ldijkman/ART-ESP32-Touch-TFT-Thermostat/images/Art_ESP32_Smart_Thermostat_webserver.jpg

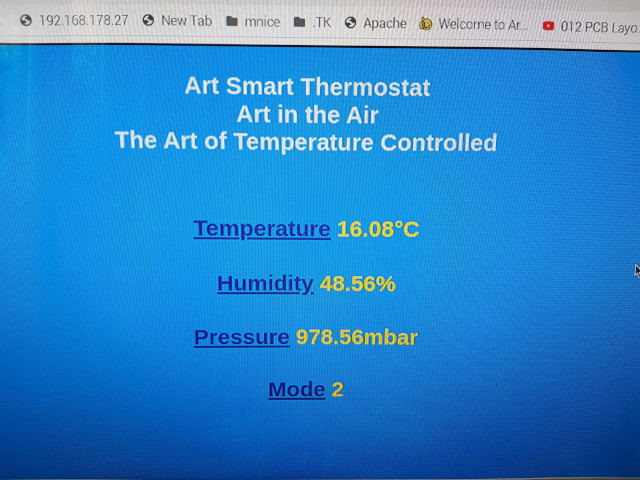
images/Art_ESP32_Smart_Thermostat_webserver.jpg
