ldijkman/ART-ESP32-Touch-TFT-Thermostat/images/art_in_the_air.jpg

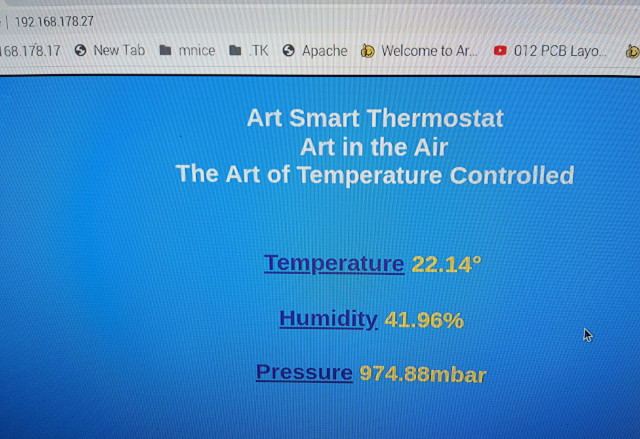
images/art_in_the_air.jpg
