ldijkman/ART-ESP32-Touch-TFT-Thermostat/images/art_ip_adres.jpg

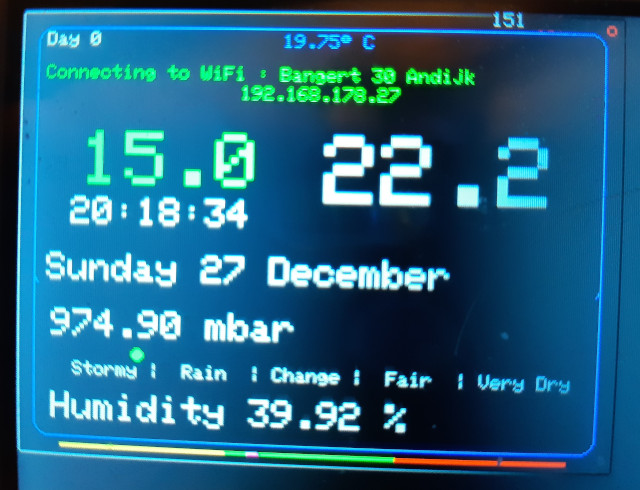
images/art_ip_adres.jpg
