ldijkman/ART-ESP32-Touch-TFT-Thermostat/images/Art_remote_mode_control.jpg

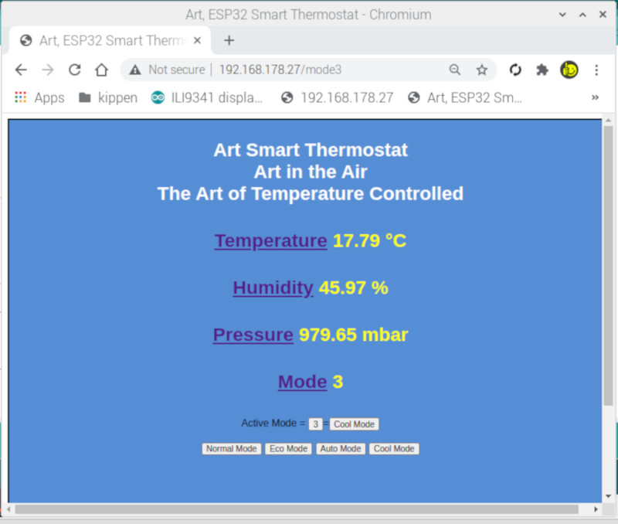
images/Art_remote_mode_control.jpg
