ldijkman/ART-ESP32-Touch-TFT-Thermostat/images/arts_memory_directory_listing.jpg

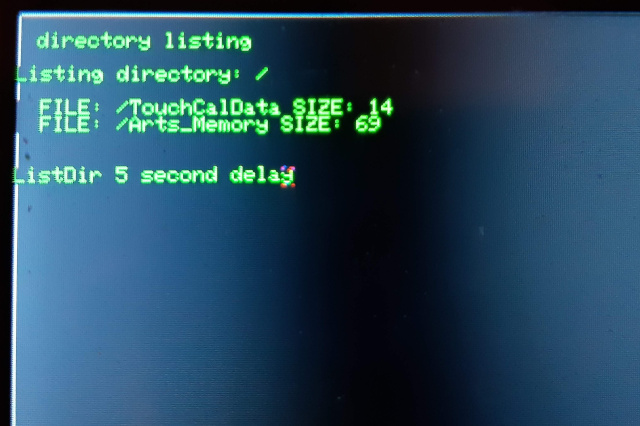
images/arts_memory_directory_listing.jpg
