ldijkman/ART-ESP32-Touch-TFT-Thermostat/images/arts_memory_save_read_write_variables_spiffs_file.jpg

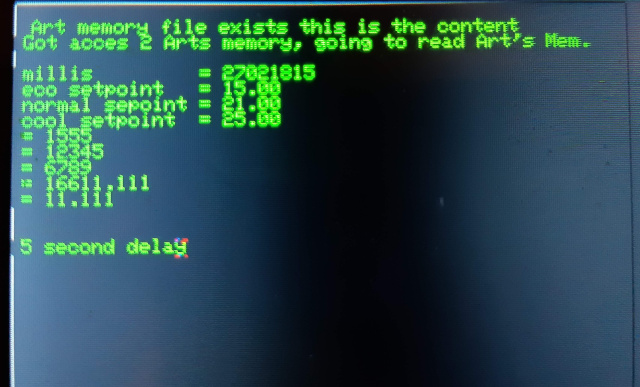
images/arts_memory_save_read_write_variables_spiffs_file.jpg
