ldijkman/ART-ESP32-Touch-TFT-Thermostat/images/ESP32-38PIN_Arduino_settings.jpg

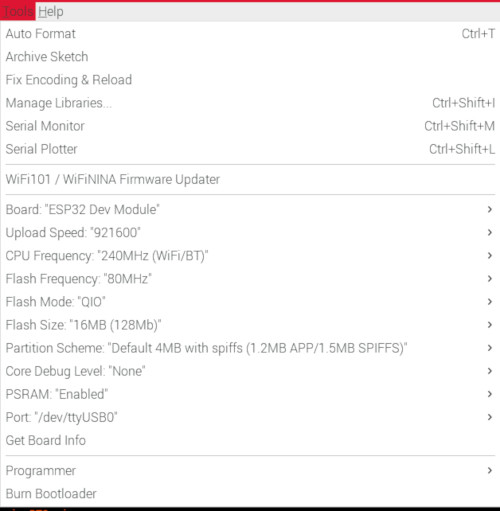
images/ESP32-38PIN_Arduino_settings.jpg
