ldijkman/ART-ESP32-Touch-TFT-Thermostat/images/screenshot-arduino-tk-alarm-DailyAlarms-com-php-1609703187235.png

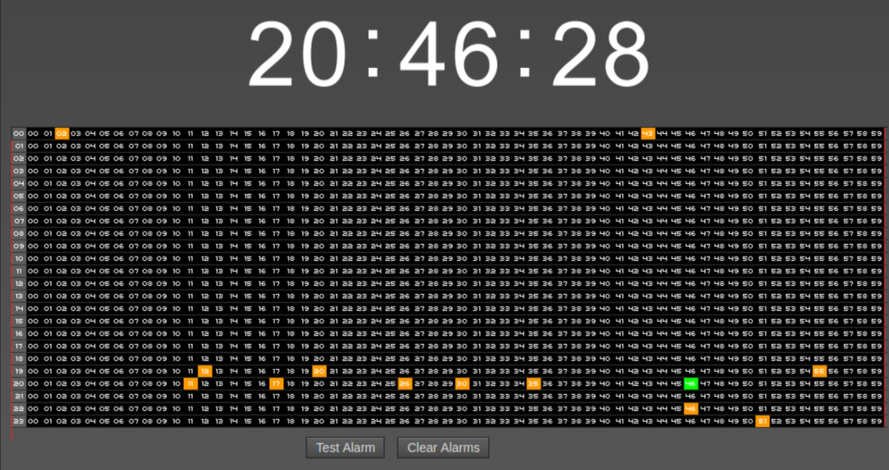
images/screenshot-arduino-tk-alarm-DailyAlarms-com-php-1609703187235.png
