ldijkman/ART-ESP32-Touch-TFT-Thermostat/test/art_test_1/Remote_WiFi_Sense_Switch/20210912_184351.jpg

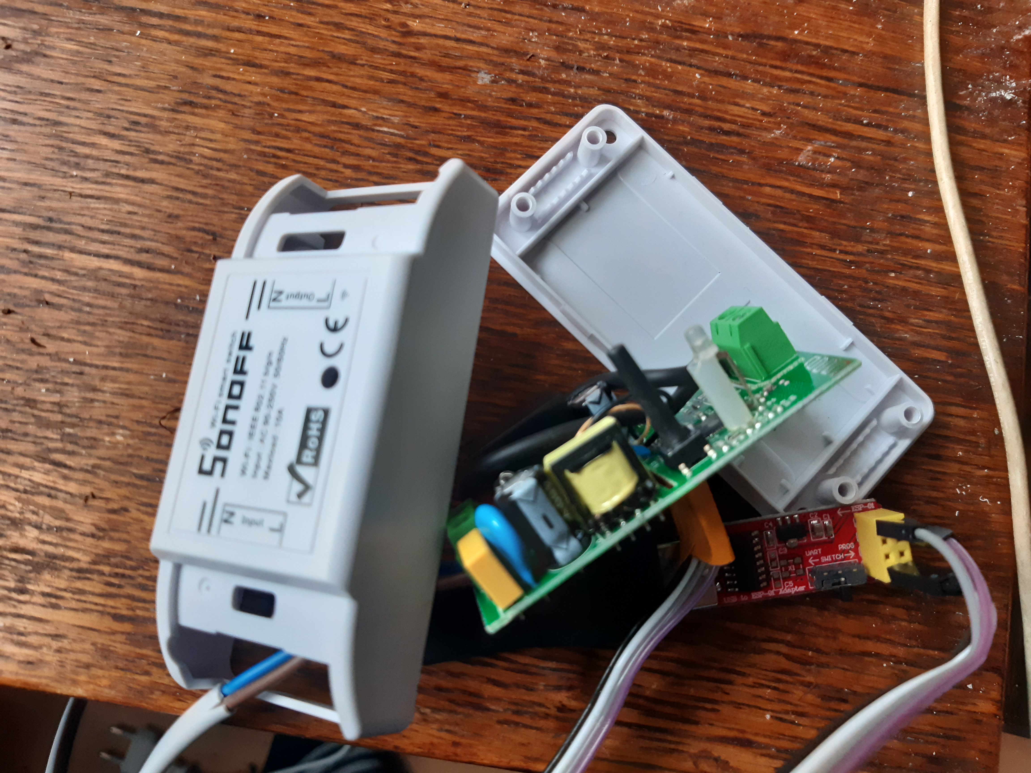
test/art_test_1/Remote_WiFi_Sense_Switch/20210912_184351.jpg
