ldijkman/ART-ESP32-Touch-TFT-Thermostat/test/art_test_1/Remote_WiFi_Sense_Switch/Screenshot_20211025-192407_Chrome.jpg

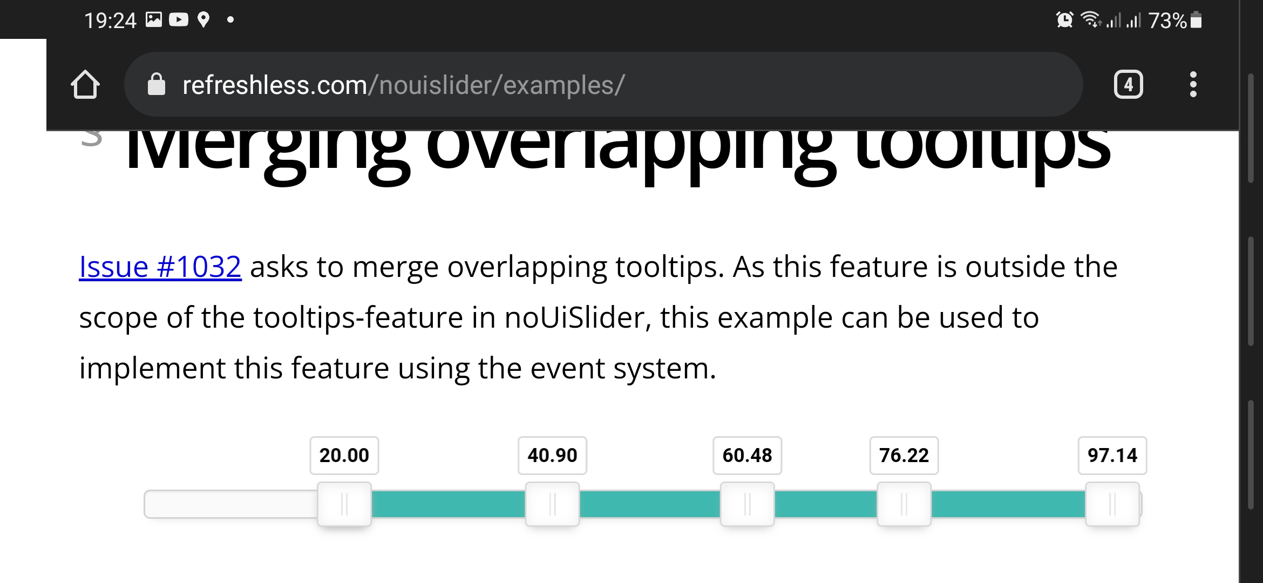
test/art_test_1/Remote_WiFi_Sense_Switch/Screenshot_20211025-192407_Chrome.jpg
