ldijkman/ART-ESP32-Touch-TFT-Thermostat/Remote_WiFi_Sense_Switch/esp8266_mdns_webserver.ino

// esp8266 remote light switch for art
// used sonoff basic wifi smart switch relais 10A
// or wemos d1 mini with relais
// why via chinese server
// reprogram it with my program
// connect usb with switch pressed to get into programming mode
// you wll loose the chinese software

// help??? should use a wiffimanager to set wifisettings for network
// and set mdns bonjour http://???????.local hostname 

// i used esp01 programmer for sonoff 
// press button sonoff when connect usb to get into programming mode (rx,tx, 3.3v, gnd.)

/*
  GPIO00 - BUTTON
  GPIO12 - RELAY
  GPIO13 - Sonoff_Relais_pin1

  GPIO03 - RX PIN
  GPIO01 - TX PIN
*/

#include <ESP8266WiFi.h>
#include <ESP8266mDNS.h>

#define ESP_getChipId()   (ESP.getChipId())

// program each esp32 or sonoff relay switch with its own easy to locate name
//const char* ServerName = "kitchen";    // http://kitchen.local     does not work on android // fing network app is handy for finding wifi ip network addresses
const char* ServerName = "hallway";      // http://hallway.local     does not work on android // fing network app is handy for finding wifi ip network addresses
//const char* ServerName = "living";     // http://living.local     does not work on android // fing network app is handy for finding wifi ip network addresses
//const char* ServerName = "garage";     // http://garage.local     does not work on android // fing network app is handy for finding wifi ip network addresses
//const char* ServerName = "bedroom";    // http://bedroom.local     does not work on android // fing network app is handy for finding wifi ip network addresses
//const char* ServerName = "stairs";     // http://stairs.local     does not work on android // fing network app is handy for finding wifi ip network addresses
//const char* ServerName = "upstairs";   // http://upstairs.local     does not work on android // fing network app is handy for finding wifi ip network addresses

const char* ssid = "Bangert_30_Andijk";       // Your Wi-Fi routerName
const char* password = "ookikwilerin";        // Your Wi-Fi router Password

String soft_ap_ssid = "ART-" + String(ServerName) + "-Light-" + String(ESP_getChipId(), HEX);    // AP accesspoint wifi name broadcasted in the air unique by chipid
const char*  soft_ap_password = "";


int value = LOW;

// think D1 is the reliscontrolpin of relayshield d1 mini
int Sonoff_Relais_pin = 5;       // relais connected to GPI05 (D1) (nodemcu / wemos d1 r1 mini
//int Sonoff_Relais_pin = 12;    // sonoff relais control pin

WiFiServer server(80);



void setup()

{

  Serial.begin(115200); //Default Baudrate

  pinMode(Sonoff_Relais_pin, OUTPUT);
  digitalWrite(Sonoff_Relais_pin, LOW);

  pinMode(13, OUTPUT);
  digitalWrite(13, HIGH);

  pinMode(0, INPUT);


  Serial.print("Connecting to the NetWork");
  WiFi.mode(WIFI_AP_STA);
  //WiFi.mode(WIFI_STA);                              // Connect to your wifi

  WiFi.softAP(soft_ap_ssid, soft_ap_password);
 
  WiFi.begin(ssid, password);
 

  WiFi.setAutoReconnect(true);
  WiFi.persistent(true);

  while (WiFi.status() != WL_CONNECTED)
  {
    digitalWrite(13, LOW );
    delay(250);
    digitalWrite(13, HIGH);
    delay(250);
    Serial.print(".");


  }

  Serial.println("WiFi connected");

  server.begin();  // Starts the Server

  Serial.println("Server started");

  while (!MDNS.begin(ServerName)) {             // Start the mDNS responder for esp8266.local
    Serial.println("Error setting up MDNS responder!");
  }
  Serial.print("mDNS responder started http://");
  Serial.print(ServerName);
  Serial.println(".local");

  MDNS.addService("http", "tcp", 80);
  Serial.println("mDNS responder started");



  Serial.print("IP Address of network: "); // will IP address on Serial Monitor

  Serial.println(WiFi.localIP());

  Serial.print("Copy and paste the following URL: https://"); // Will print IP address in URL format

  Serial.print(WiFi.localIP());

  Serial.println("/");

}



void loop() {
  MDNS.update();

  if (digitalRead(0) == LOW) {               // manual control on/off toggle light with pushbutton on sonoff
    while (digitalRead(0) == LOW) {
      /*wait for button release*/
    }
    if (value == LOW) {
      digitalWrite(Sonoff_Relais_pin, HIGH); // Turn Sonoff_Relais_pin ON
      value = HIGH;
      digitalWrite(13, LOW);
    }
    else {
      digitalWrite(Sonoff_Relais_pin, LOW); // Turn Sonoff_Relais_pin OFF
      value = LOW;
      digitalWrite(13, HIGH);
    }

  }

  WiFiClient client = server.available();

  if (!client)

  {

    return;

  }

  Serial.println("Waiting for new client");

  while (!client.available())
  {
    delay(1);
  }



  String request = client.readStringUntil('\r');

  Serial.println(request);

  client.flush();

  if (request.indexOf("/value") != -1)
  {
    client.println("HTTP/1.1 200 OK"); //
    client.println("Content-Type: text/html");
    client.println("");
    //client.println("<!DOCTYPE HTML>");
    //client.println("<html>");
    client.println(value); //
    return;
  }



  if (request.indexOf("/LED=ON") != -1)
  {
    digitalWrite(Sonoff_Relais_pin, HIGH); // Turn Sonoff_Relais_pin ON
    value = HIGH;
    digitalWrite(13, LOW  );
  }

  if (request.indexOf("/LED=OFF") != -1)
  {
    digitalWrite(Sonoff_Relais_pin, LOW); // Turn Sonoff_Relais_pin OFF
    value = LOW;
    digitalWrite(13, HIGH);
  }



  //*------------------HTML Page Code---------------------*//
  client.println("HTTP/1.1 200 OK"); //
  client.println("Content-Type: text/html");
  client.println("");
  client.println("<!DOCTYPE HTML>");
  client.println("<html>");
  client.print("<meta http-equiv=\"refresh\" content=\"5; URL=http://");
  client.print(WiFi.localIP());
  client.print("\">");
  client.print("<body><center><h4>");
  client.print(" LIGHT = ");

  if (value == HIGH)
  {
    client.print("ON</h4>");
    client.println("<a href=\"/LED=OFF\"\"><button style=\"height:160px; width:320px; background-color:yellow;\"><h1> Turn OFF </h1></button></a>");
  }
  else
  {
    client.print("OFF</h4>");
    client.println("<a href=\"/LED=ON\"\"><button style=\"height:160px; width:320px; background-color:gray;\"><h1>  Turn ON  </h1></button></a>");
  }
  client.print("<a href=\"http://");
  client.print(ServerName);
  client.print(".local\"><h4>http://");
  client.print(ServerName);
  client.println(".local</h4></a>");


  client.print("<a href=\"http://");
  client.print(WiFi.localIP());
  client.print("\"><h4>http://");
  client.print(WiFi.localIP());
  client.println("</h4></a>");

  client.println("</center></body></html>");



  delay(1);

  Serial.println("Client disonnected");

  Serial.println("");

}
