ldijkman/ART-ESP32-Touch-TFT-Thermostat/test/ESP32 RTC DS3231 RealTimeClock.ino

// ESP32 I2C RTC DS3231 realtimeclock test
// sets the time on DS3231 from computer when progam loads
// and print inforation about time and date to serial monitor
// software i2c on other i/o = non hardware i2c
// ART ESP32Thermostat by luberth dijkman
// https://oshwlab.com/l.dijkman/esp32-dev-kit-38-pin-to-spi-touch-tft 
// https://github.com/ldijkman/ART-ESP32-Touch-TFT-Thermostat 
// http://www.Arduino.TK

#include <Wire.h> 

#define I2C_SDA 33  //gpio33
#define I2C_SCL 32  //gpio32

#include "RTClib.h" // https://github.com/adafruit/RTClib
RTC_DS3231 rtc;     // download zip from above and install library from zip

char daysOfTheWeek[7][12] = {"Sunday", "Monday", "Tuesday", "Wednesday", "Thursday", "Friday", "Saturday"};

void setup(void) {

  Wire.begin(I2C_SDA, I2C_SCL);

  Serial.begin(115200);

  if (! rtc.begin()) {
    Serial.println("Couldn't find RTC");
    Serial.flush();
    abort();
  }

  if (rtc.lostPower()) {
    Serial.println("RTC lost power, let's set the time!");
    // When time needs to be set on a new device, or after a power loss, the
    // following line sets the RTC to the date & time this sketch was compiled
    rtc.adjust(DateTime(F(__DATE__), F(__TIME__)));
    // This line sets the RTC with an explicit date & time, for example to set
    // January 21, 2014 at 3am you would call:
    // rtc.adjust(DateTime(2014, 1, 21, 3, 0, 0));
  }

  // When time needs to be re-set on a previously configured device, the
  // following line sets the RTC to the date & time this sketch was compiled
  // rtc.adjust(DateTime(F(__DATE__), F(__TIME__)));
  // This line sets the RTC with an explicit date & time, for example to set
  // January 21, 2014 at 3am you would call:
  // rtc.adjust(DateTime(2014, 1, 21, 3, 0, 0));
}

void loop () {
    DateTime now = rtc.now();

    Serial.print(now.year(), DEC);
    Serial.print('/');
    Serial.print(now.month(), DEC);
    Serial.print('/');
    Serial.print(now.day(), DEC);
    Serial.print(" (");
    Serial.print(daysOfTheWeek[now.dayOfTheWeek()]);
    Serial.print(") ");
    Serial.print(now.hour(), DEC);
    Serial.print(':');
    Serial.print(now.minute(), DEC);
    Serial.print(':');
    Serial.print(now.second(), DEC);
    Serial.println();

    Serial.print("Temperature: ");
    Serial.print(rtc.getTemperature());
    Serial.println(" C");

    Serial.println();
    delay(1000);
}
