ldijkman/ART-ESP32-Touch-TFT-Thermostat/test/ESP32 Passive Buzzer Test PWM output.ino

// ESP32 KY-006 passive buzzer test
// https://oshwlab.com/l.dijkman/esp32-dev-kit-38-pin-to-spi-touch-tft 
// https://github.com/ldijkman/ART-ESP32-Touch-TFT-Thermostat 
// http://www.Arduino.TK

#include <Tone32.h> //https://github.com/lbernstone/Tone32

#define BUZZER_PIN 12  //gpio 12  signal and ground for KY-006 Passive buzzer module
#define BUZZER_CHANNEL 0

void setup() {

}

void loop() {
  tone(BUZZER_PIN, NOTE_C4, 500, BUZZER_CHANNEL);
  noTone(BUZZER_PIN, BUZZER_CHANNEL);
  tone(BUZZER_PIN, NOTE_D4, 500, BUZZER_CHANNEL);
  noTone(BUZZER_PIN, BUZZER_CHANNEL);
  tone(BUZZER_PIN, NOTE_E4, 500, BUZZER_CHANNEL);
  noTone(BUZZER_PIN, BUZZER_CHANNEL);
  tone(BUZZER_PIN, NOTE_F4, 500, BUZZER_CHANNEL);
  noTone(BUZZER_PIN, BUZZER_CHANNEL);
  tone(BUZZER_PIN, NOTE_G4, 500, BUZZER_CHANNEL);
  noTone(BUZZER_PIN, BUZZER_CHANNEL);
  tone(BUZZER_PIN, NOTE_A4, 500, BUZZER_CHANNEL);
  noTone(BUZZER_PIN, BUZZER_CHANNEL);
  tone(BUZZER_PIN, NOTE_B4, 500, BUZZER_CHANNEL);
  noTone(BUZZER_PIN, BUZZER_CHANNEL);
}
