ldijkman/ART-ESP32-Touch-TFT-Thermostat/test/touch_calibrate.ino

// hello
// https://oshwlab.com/l.dijkman/esp32-dev-kit-38-pin-to-spi-touch-tft
// https://github.com/ldijkman/ART-ESP32-Touch-TFT-Thermostat
// http://www.Arduino.TK
//
// https://m.facebook.com/groups/2643123052617990
// https://www.facebook.com/groups/esp32smartthermostat
//
// GNU General Public License,
// which basically means that you may freely copy, change, and distribute it,
// but you may not impose any restrictions on further distribution,
// and you must make the source code available.
//

void touch_calibrate()
{
  uint16_t calData[5];
  uint8_t calDataOK = 0;
  Serial.println("funtion calibrate");
  // check file system exists
  if (!SPIFFS.begin()) {
    Serial.println("Formating file system");
    SPIFFS.format();
    SPIFFS.begin();
  }

  // check if calibration file exists and size is correct
  if (SPIFFS.exists(CALIBRATION_FILE)) {
    if (REPEAT_CAL)
    {
      // Delete if we want to re-calibrate
      SPIFFS.remove(CALIBRATION_FILE);
    }
    else
    {
      File f = SPIFFS.open(CALIBRATION_FILE, "r");
      if (f) {
        if (f.readBytes((char *)calData, 14) == 14)
          calDataOK = 1;
        f.close();
      }
    }
  }

  if (calDataOK && !REPEAT_CAL) {
    // calibration data valid
    tft.setTouch(calData);
  } else {
    // data not valid so recalibrate
    tft.fillScreen(TFT_BLACK);
    tft.setCursor(20, 20);
    tft.setTextFont(1);
    tft.setTextSize(2);
    tft.setTextColor(TFT_WHITE, TFT_BLACK);

    tft.println("Touch corners as indicated");

    tft.setTextFont(1);
    tft.println();

    if (REPEAT_CAL) {
      tft.setTextColor(TFT_RED, TFT_BLACK);
      tft.println("Set REPEAT_CAL to false");
      tft.println("to stop this running again!");
    }

    tft.calibrateTouch(calData, GREEN, TFT_BLACK, 25);

    tft.fillScreen(TFT_BLACK);
    tft.drawRoundRect(1, 1, 319, 239, 2, DARKGREY);
    tft.setTextColor(TFT_GREEN, TFT_BLACK);
    tft.setCursor(30, 110);
    tft.println("Calibration complete!");
    delay(4000);
    tft.fillScreen(BLACK);

    // store data
    File f = SPIFFS.open(CALIBRATION_FILE, "w");
    if (f) {
      f.write((const unsigned char *)calData, 14);
      f.close();
    }
  }
}
